hegars/USBtoMIDI/images/d8b_midi_breakout_2.jpg

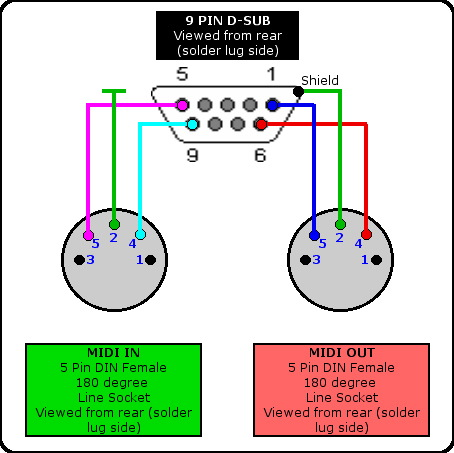
images/d8b_midi_breakout_2.jpg
