hegars/USBtoMIDI/images/midi.gif

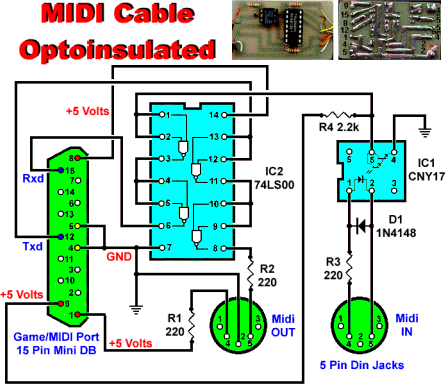
images/midi.gif
