hegars/USBtoMIDI/images/unnamed (1).gif

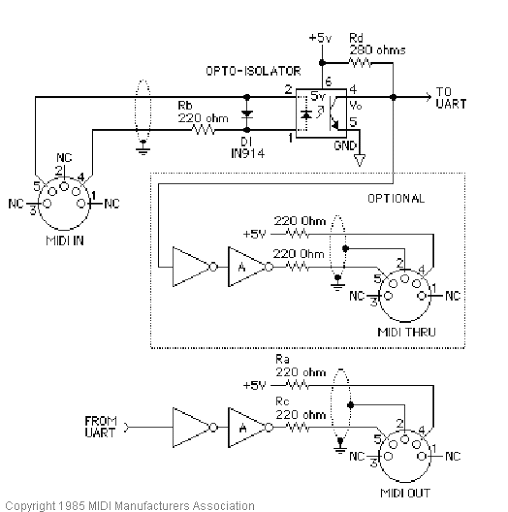
images/unnamed (1).gif
