hegars/USBtoMIDI/images/unnamed.gif

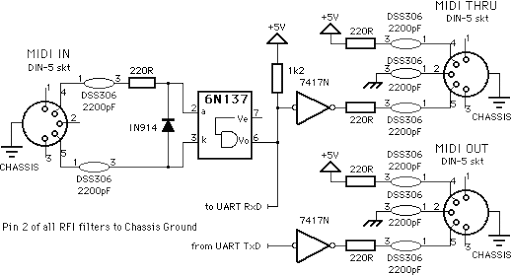
images/unnamed.gif
